danelynnn/ktane/processing/program/data/img/1-copyright.png

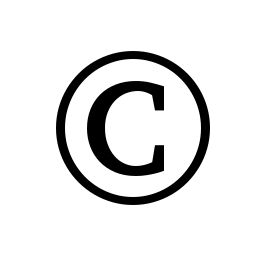
processing/program/data/img/1-copyright.png
