danelynnn/ktane/processing/program/data/img/2-filledstar.png

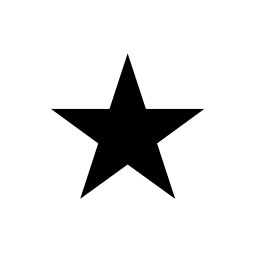
processing/program/data/img/2-filledstar.png
