danelynnn/ktane/processing/program/data/img/3-hollowstar.png

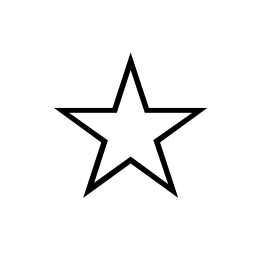
processing/program/data/img/3-hollowstar.png
