danelynnn/ktane/processing/program/data/img/4-smileyface.png

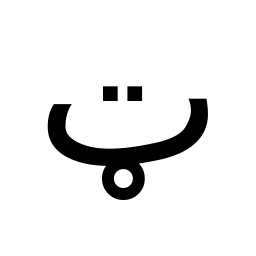
processing/program/data/img/4-smileyface.png
