danelynnn/ktane/processing/program/data/img/5-doublek.png

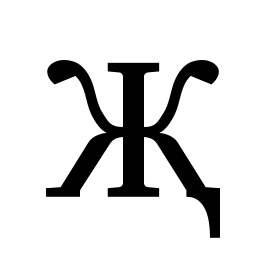
processing/program/data/img/5-doublek.png
