danelynnn/ktane/processing/program/data/img/6-omega.png

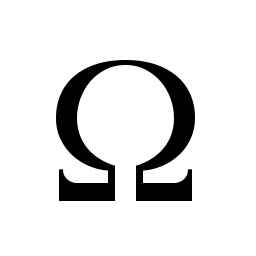
processing/program/data/img/6-omega.png
