danelynnn/ktane/processing/program/data/img/7-squidknife.png

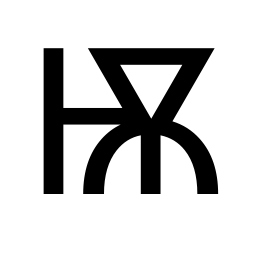
processing/program/data/img/7-squidknife.png
