danelynnn/ktane/processing/program/data/img/8-pumpkin.png

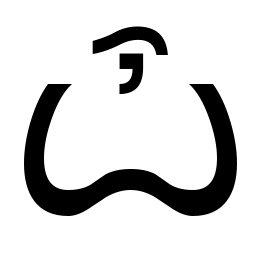
processing/program/data/img/8-pumpkin.png
