danelynnn/ktane/processing/program/data/img/9-hookn.png

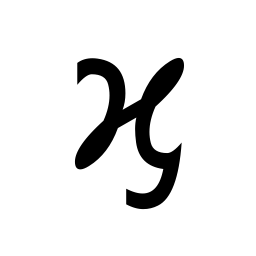
processing/program/data/img/9-hookn.png
