danelynnn/ktane/processing/program/data/img/11-six.png

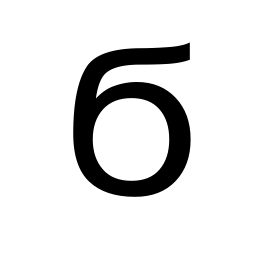
processing/program/data/img/11-six.png
