danelynnn/ktane/processing/program/data/img/12-squigglyn.png

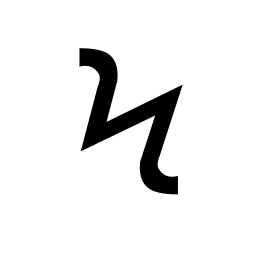
processing/program/data/img/12-squigglyn.png
