danelynnn/ktane/processing/program/data/img/13-at.png

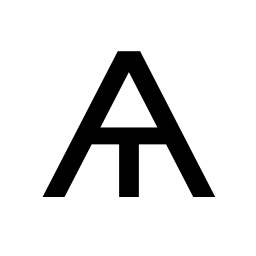
processing/program/data/img/13-at.png
