danelynnn/ktane/processing/program/data/img/14-ae.png

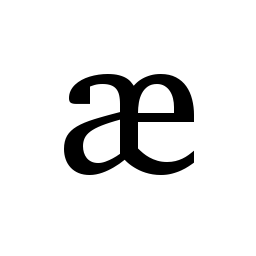
processing/program/data/img/14-ae.png
