danelynnn/ktane/processing/program/data/img/15-meltedthree.png

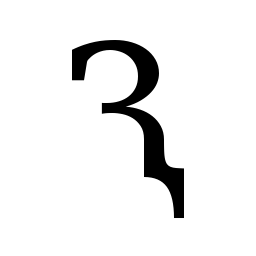
processing/program/data/img/15-meltedthree.png
