danelynnn/ktane/processing/program/data/img/16-euro.png

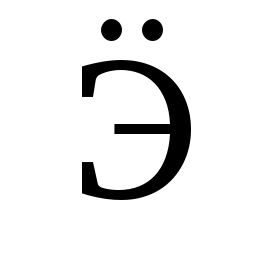
processing/program/data/img/16-euro.png
