danelynnn/ktane/processing/program/data/img/18-nwithhat.png

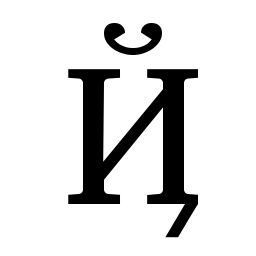
processing/program/data/img/18-nwithhat.png
