danelynnn/ktane/processing/program/data/img/19-dragon.png

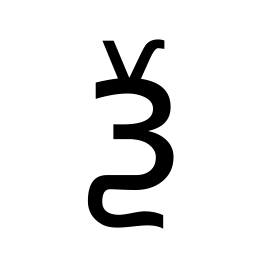
processing/program/data/img/19-dragon.png
