danelynnn/ktane/processing/program/data/img/20-questionmark.png

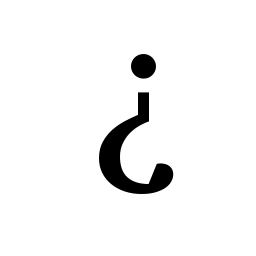
processing/program/data/img/20-questionmark.png
