danelynnn/ktane/processing/program/data/img/21-paragraph.png

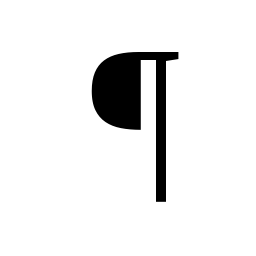
processing/program/data/img/21-paragraph.png
