danelynnn/ktane/processing/program/data/img/22-rightc.png

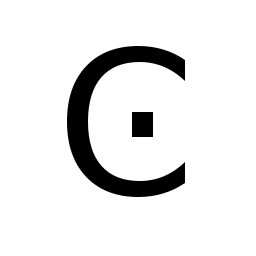
processing/program/data/img/22-rightc.png
