danelynnn/ktane/processing/program/data/img/23-leftc.png

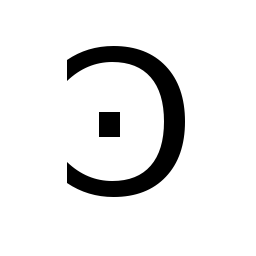
processing/program/data/img/23-leftc.png
