danelynnn/ktane/processing/program/data/img/24-pitchfork.png

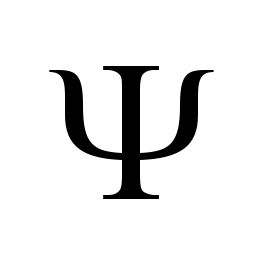
processing/program/data/img/24-pitchfork.png
