danelynnn/ktane/processing/program/data/img/26-cursive.png

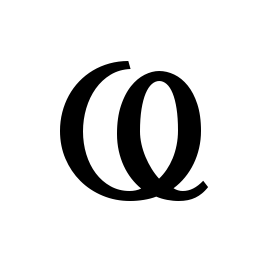
processing/program/data/img/26-cursive.png
