danelynnn/ktane/processing/program/data/img/27-tracks.png

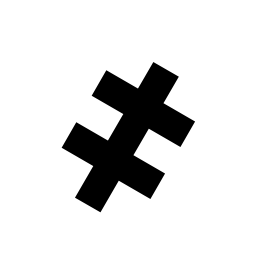
processing/program/data/img/27-tracks.png
