danelynnn/ktane/processing/program/data/img/28-balloon.png

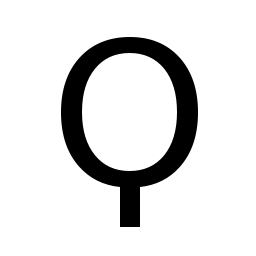
processing/program/data/img/28-balloon.png
