danelynnn/ktane/processing/program/data/img/30-upsidedowny.png

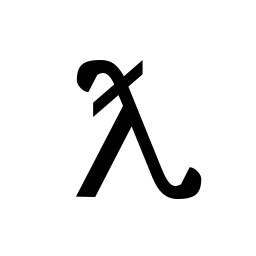
processing/program/data/img/30-upsidedowny.png
