danelynnn/ktane/processing/program/data/img/31-bt.png

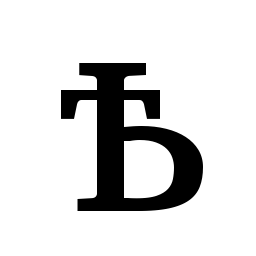
processing/program/data/img/31-bt.png
